AdrianaCabrera/MyOrthotics-2.0/images/image1.png

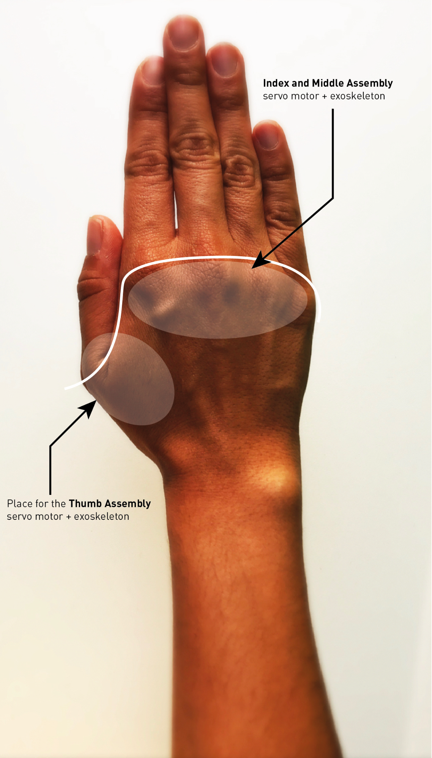
images/image1.png
