AdrianaCabrera/MyOrthotics-2.0/images/image2.png

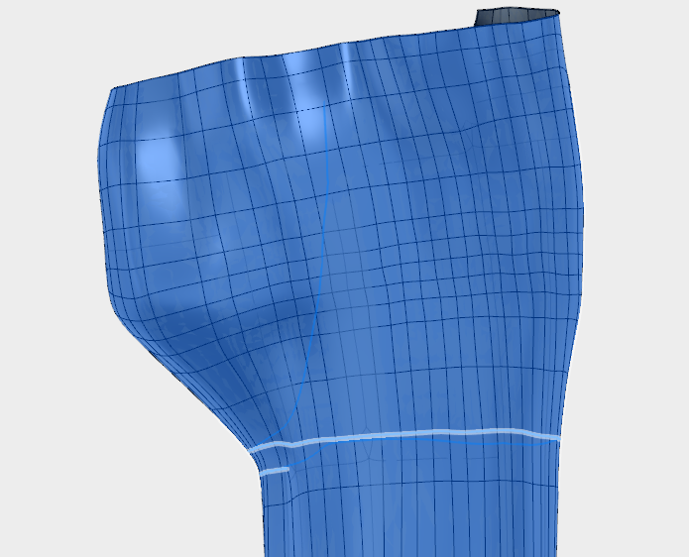
images/image2.png
