AdrianaCabrera/MyOrthotics-2.0/images/image3.jpg

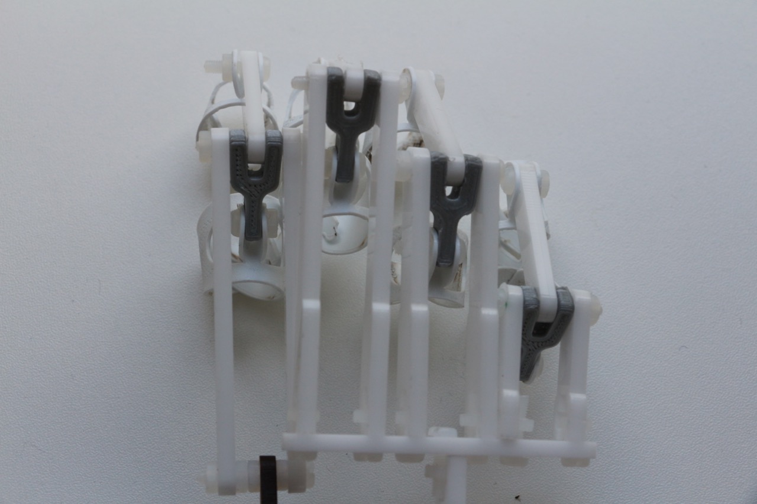
images/image3.jpg
