AdrianaCabrera/MyOrthotics-2.0/images/image4.png

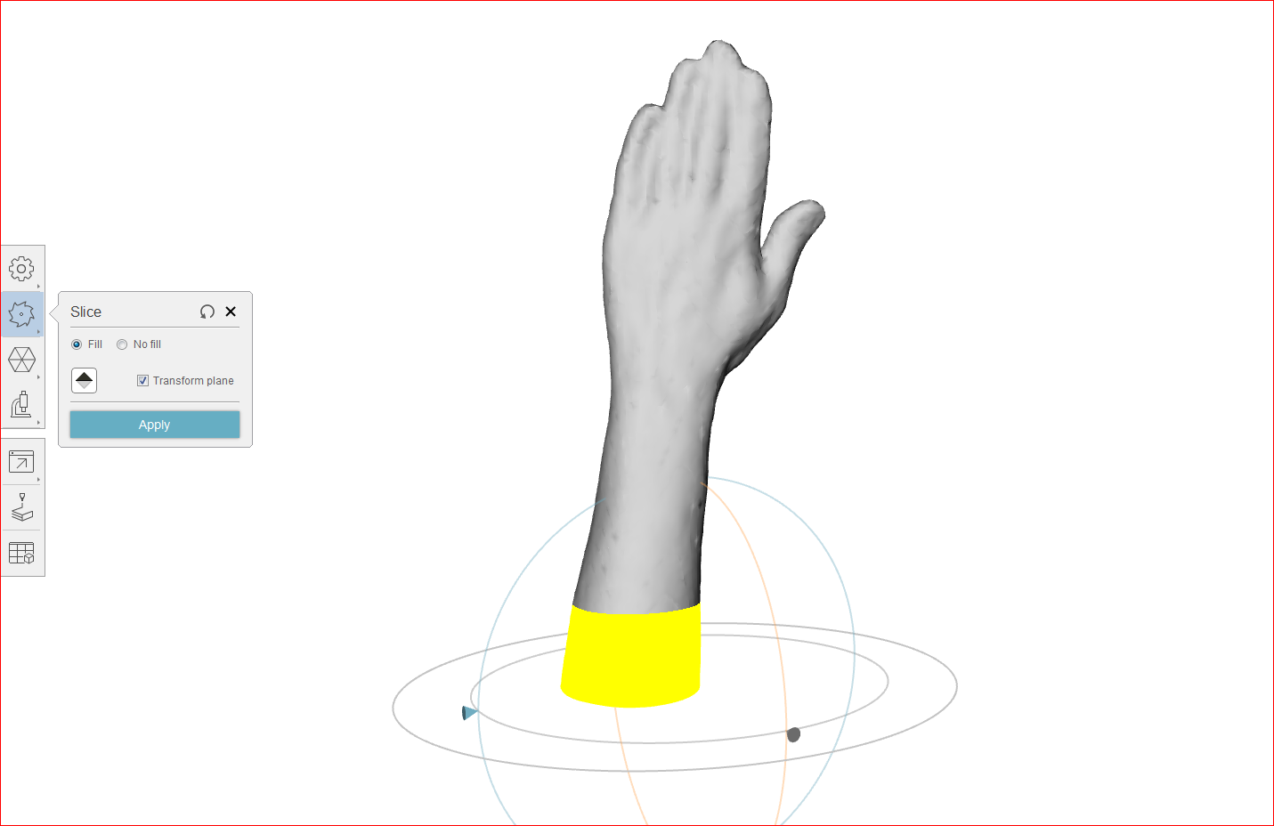
images/image4.png
