AdrianaCabrera/MyOrthotics-2.0/images/image6.png

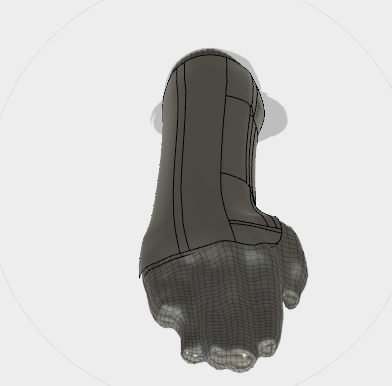
images/image6.png
