AdrianaCabrera/MyOrthotics-2.0/images/image7.png

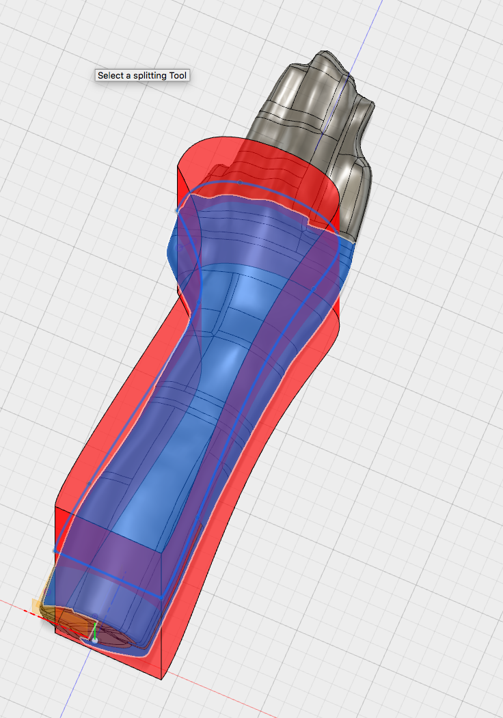
images/image7.png
