AdrianaCabrera/MyOrthotics-2.0/images/image8.png

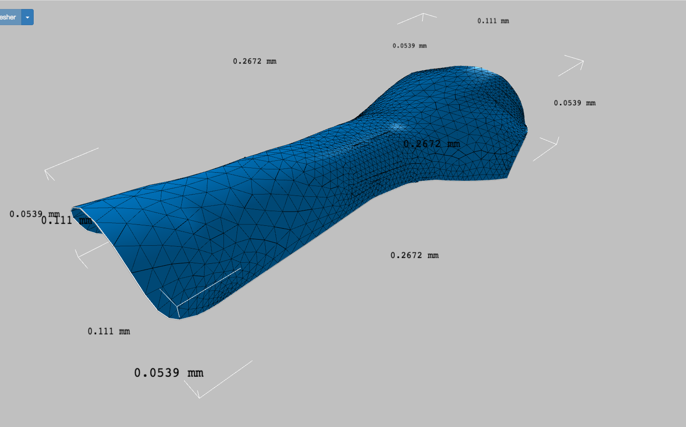
images/image8.png
