AdrianaCabrera/MyOrthotics-2.0/images/image9.jpg

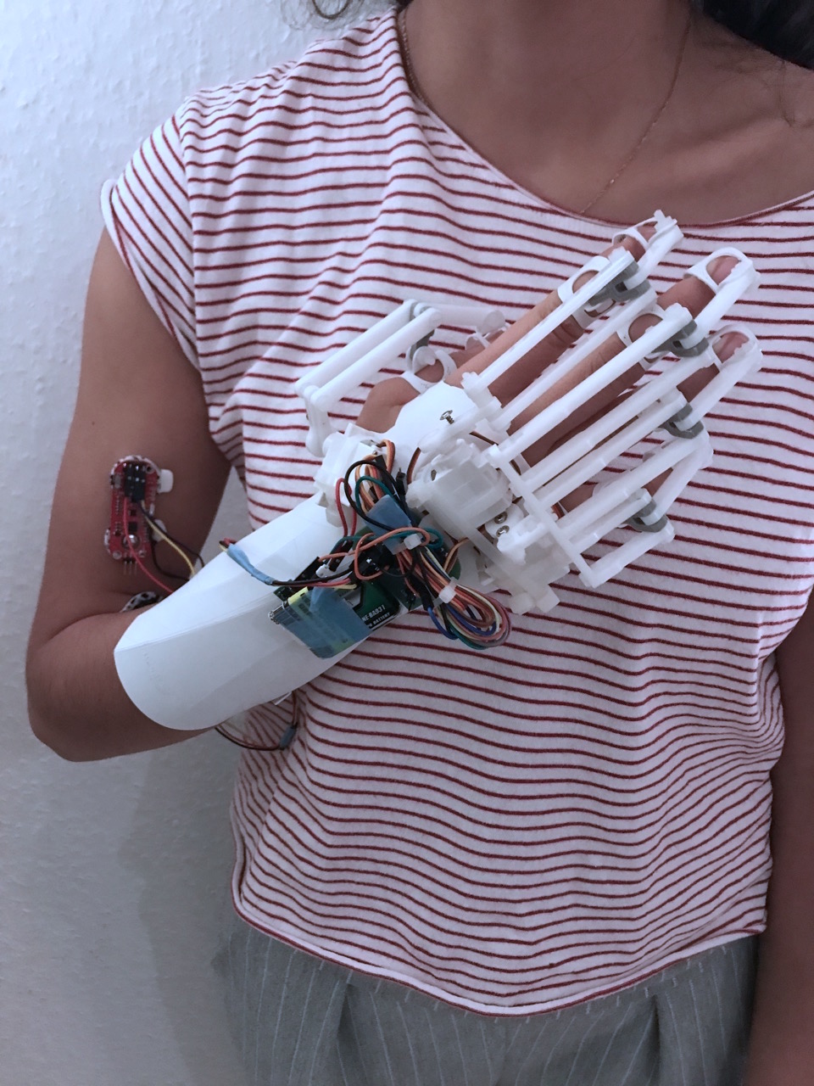
images/image9.jpg
