AdrianaCabrera/MyOrthotics-2.0/images/image10.png

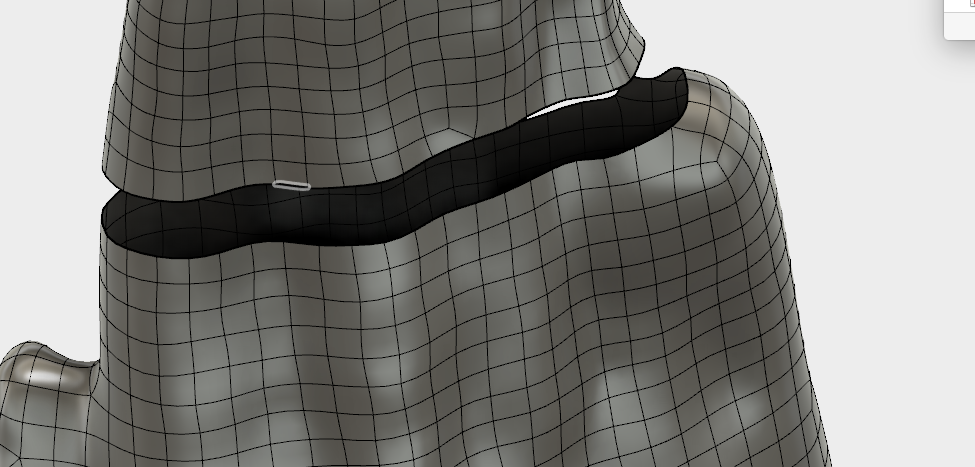
images/image10.png
