AdrianaCabrera/MyOrthotics-2.0/images/image11.png

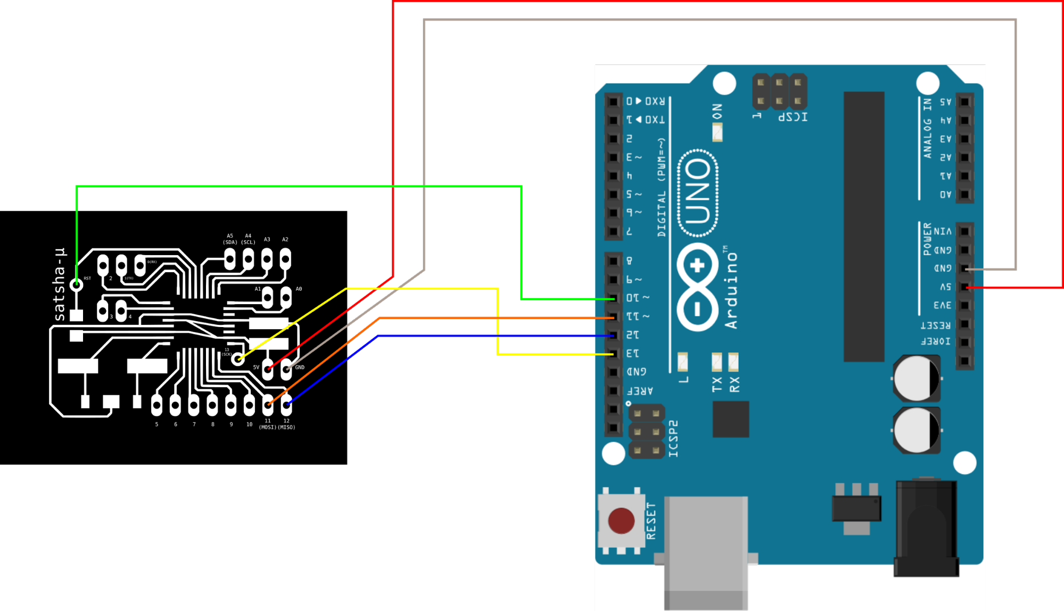
images/image11.png
