AdrianaCabrera/MyOrthotics-2.0/images/image12.png

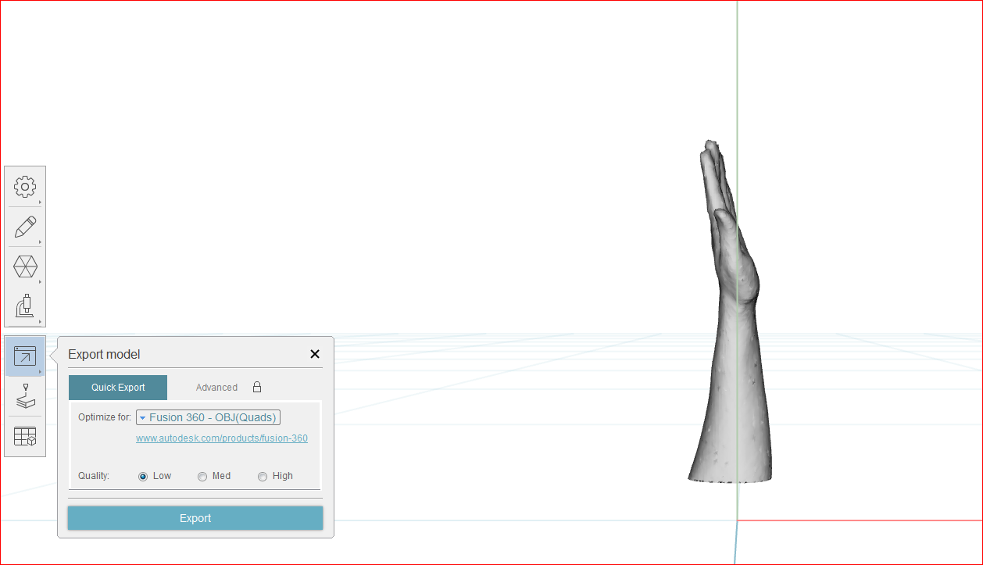
images/image12.png
