AdrianaCabrera/MyOrthotics-2.0/images/image13.jpg

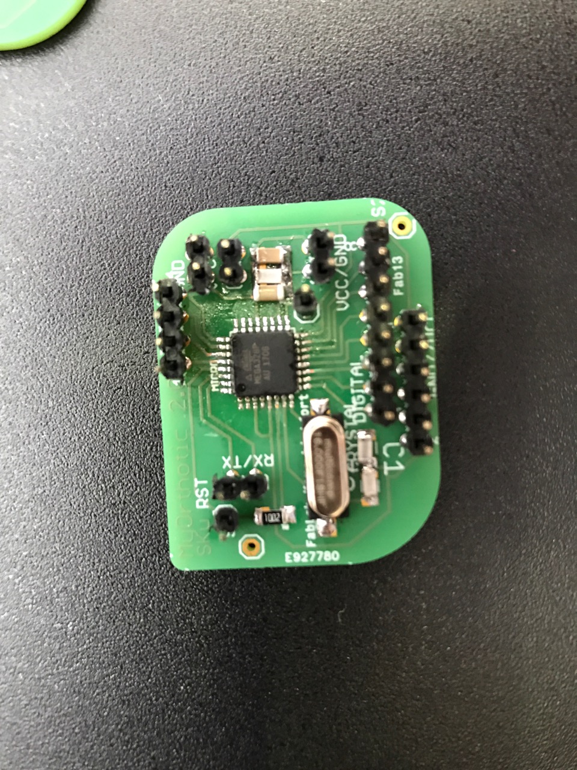
images/image13.jpg
