AdrianaCabrera/MyOrthotics-2.0/images/image14.jpg

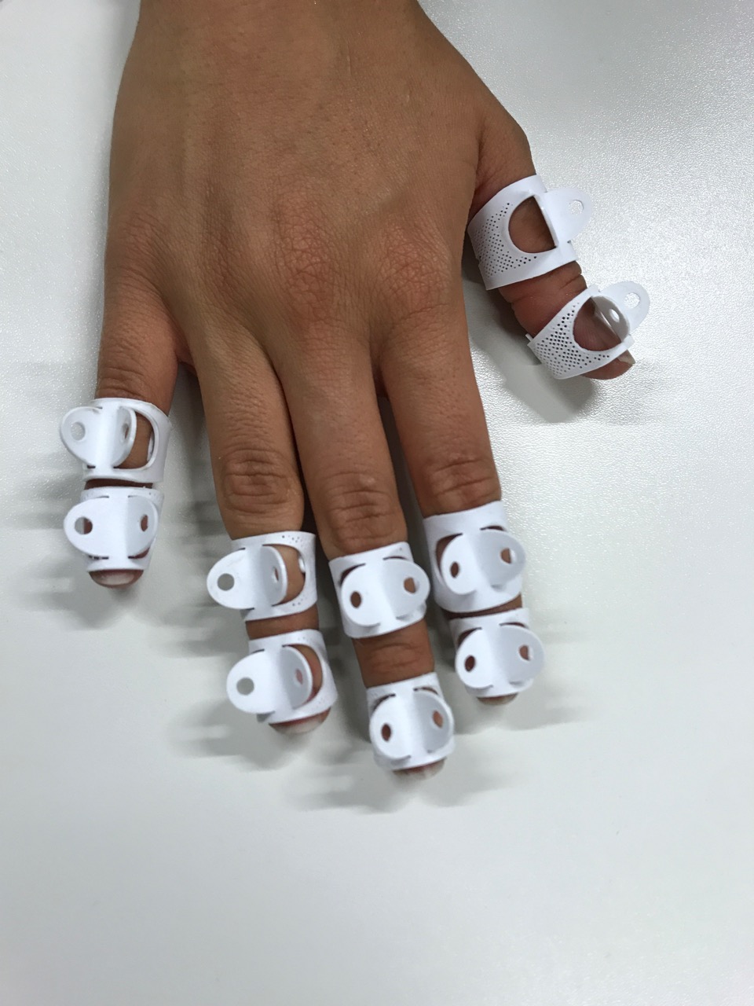
images/image14.jpg
