AdrianaCabrera/MyOrthotics-2.0/images/image15.png

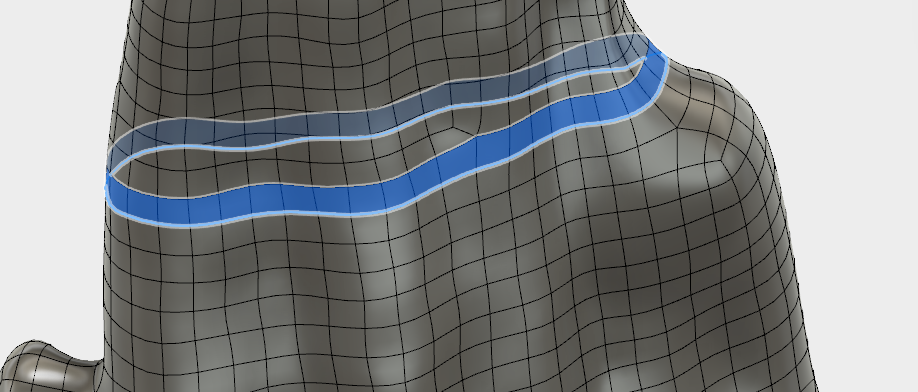
images/image15.png
