AdrianaCabrera/MyOrthotics-2.0/images/image16.png

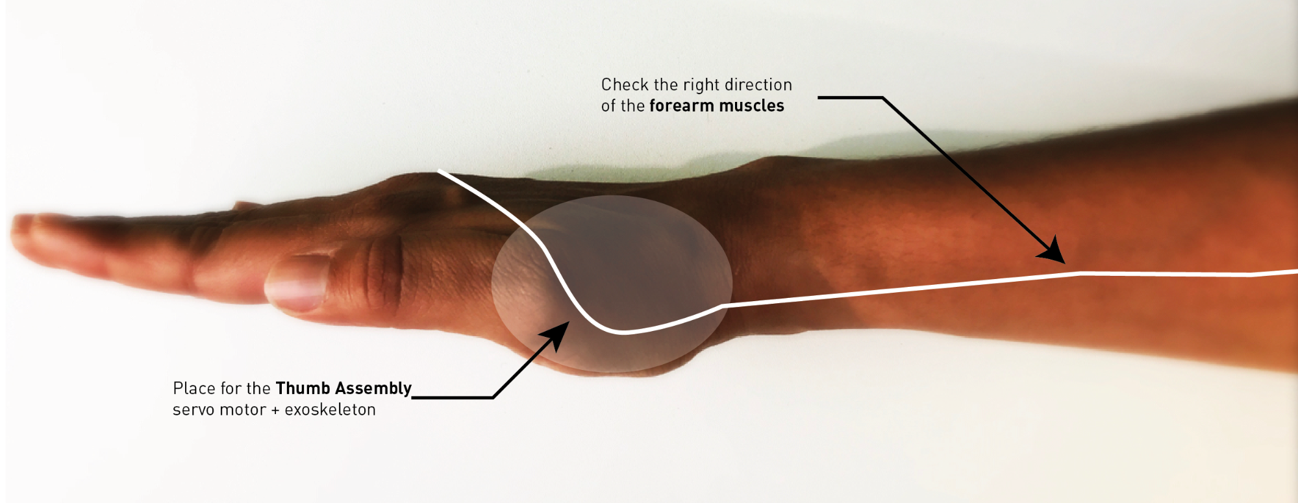
images/image16.png
