AdrianaCabrera/MyOrthotics-2.0/images/image17.png

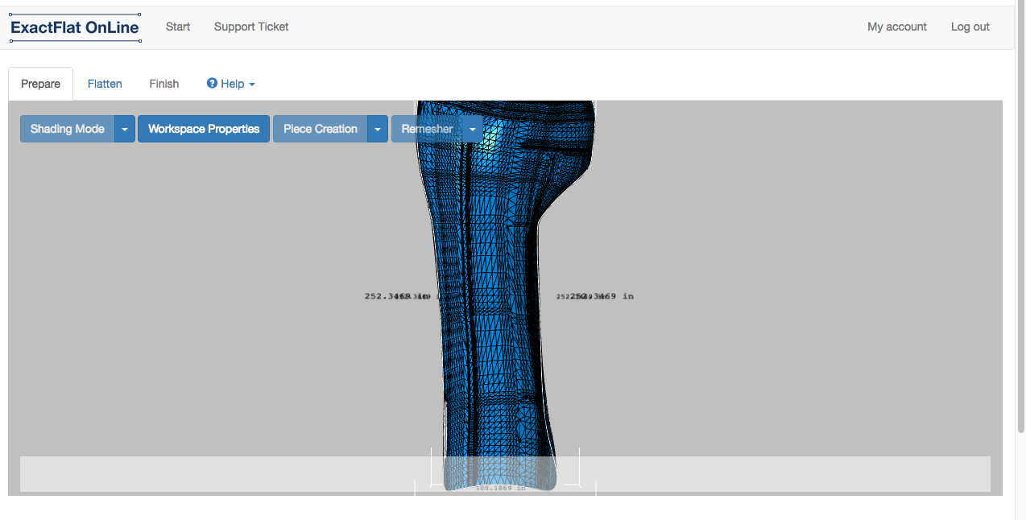
images/image17.png
