AdrianaCabrera/MyOrthotics-2.0/images/image19.png

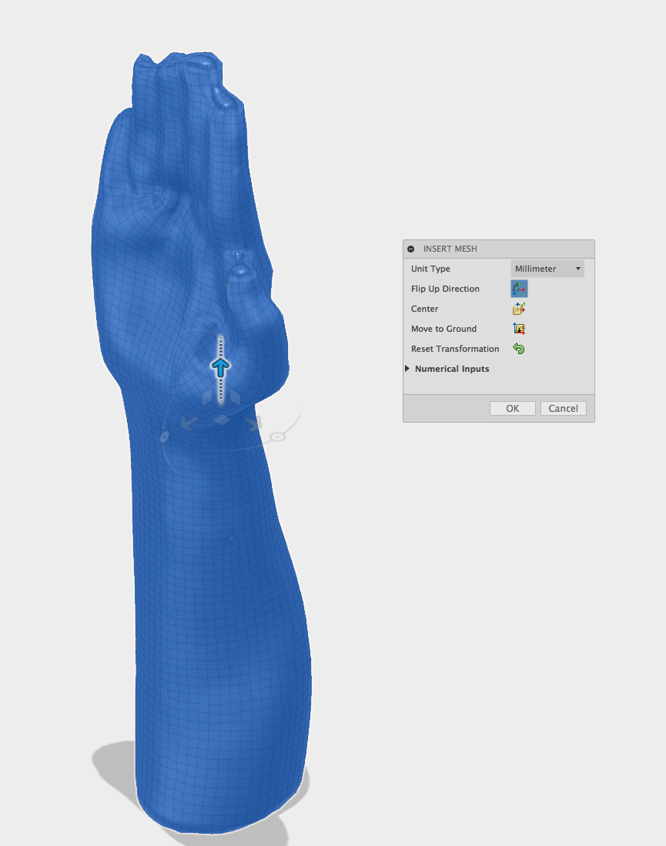
images/image19.png
