AdrianaCabrera/MyOrthotics-2.0/images/image20.png

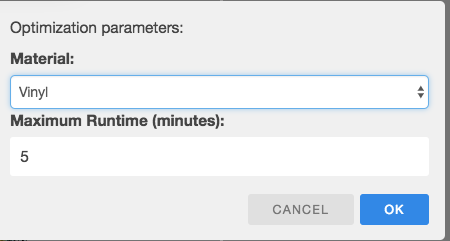
images/image20.png
