AdrianaCabrera/MyOrthotics-2.0/images/image21.jpg

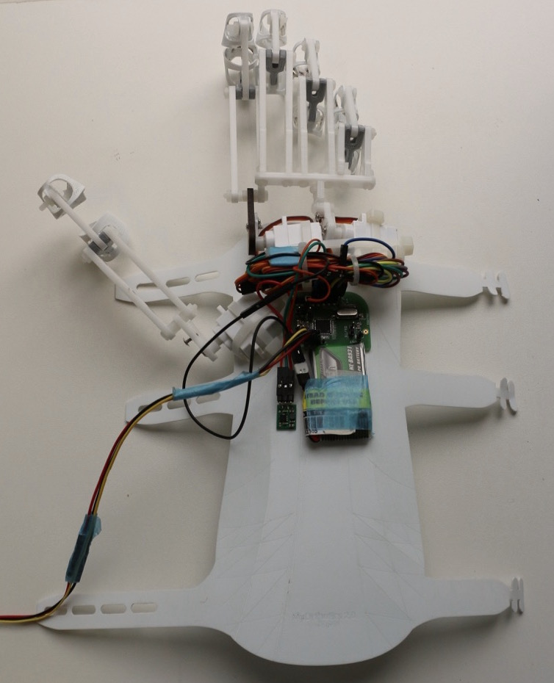
images/image21.jpg
