AdrianaCabrera/MyOrthotics-2.0/images/image22.png

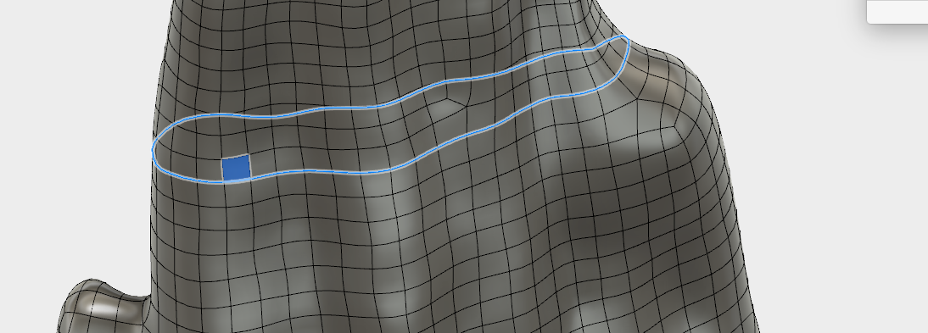
images/image22.png
