AdrianaCabrera/MyOrthotics-2.0/images/image23.jpg

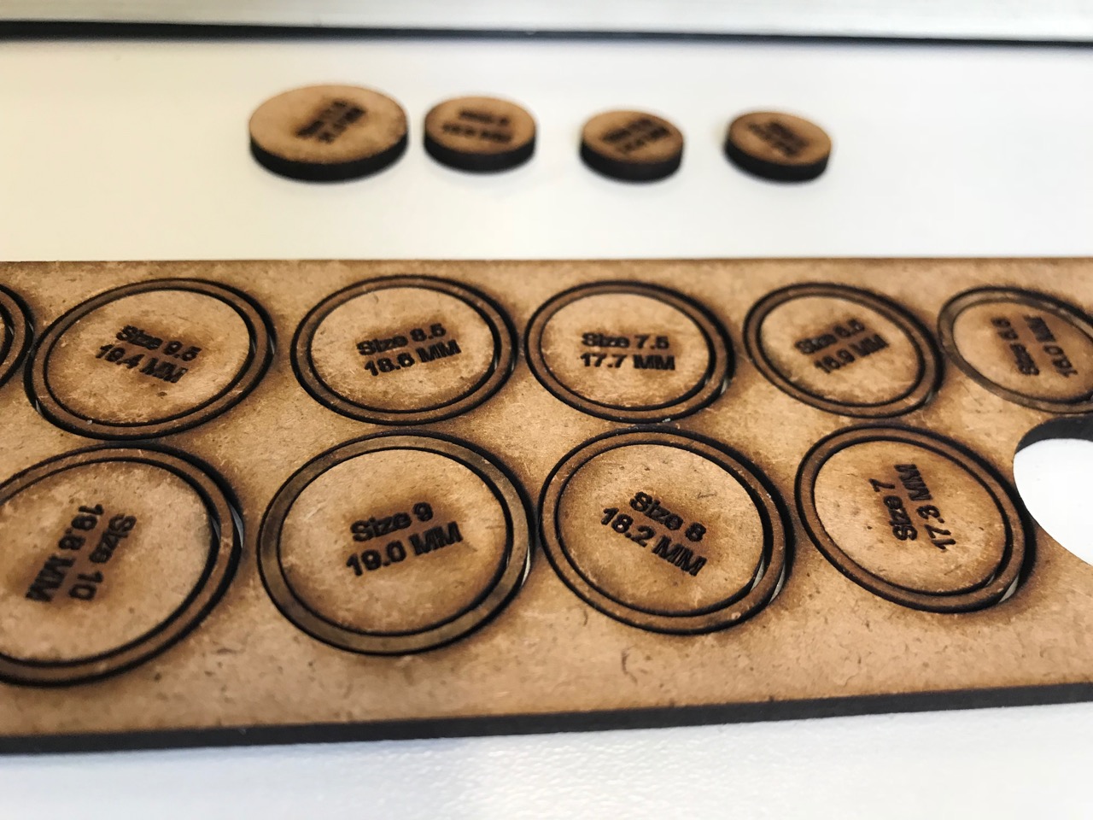
images/image23.jpg
