AdrianaCabrera/MyOrthotics-2.0/images/image24.jpg

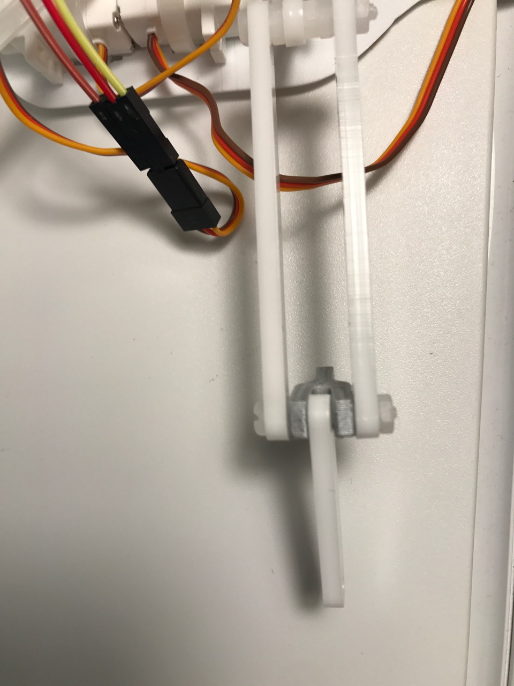
images/image24.jpg
