AdrianaCabrera/MyOrthotics-2.0/images/image25.png

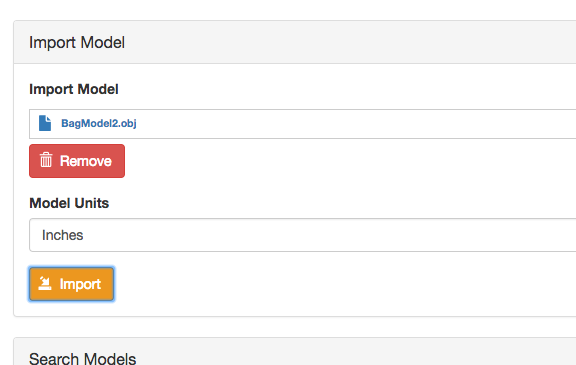
images/image25.png
