AdrianaCabrera/MyOrthotics-2.0/images/image26.png

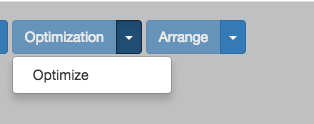
images/image26.png
