AdrianaCabrera/MyOrthotics-2.0/images/image28.jpg

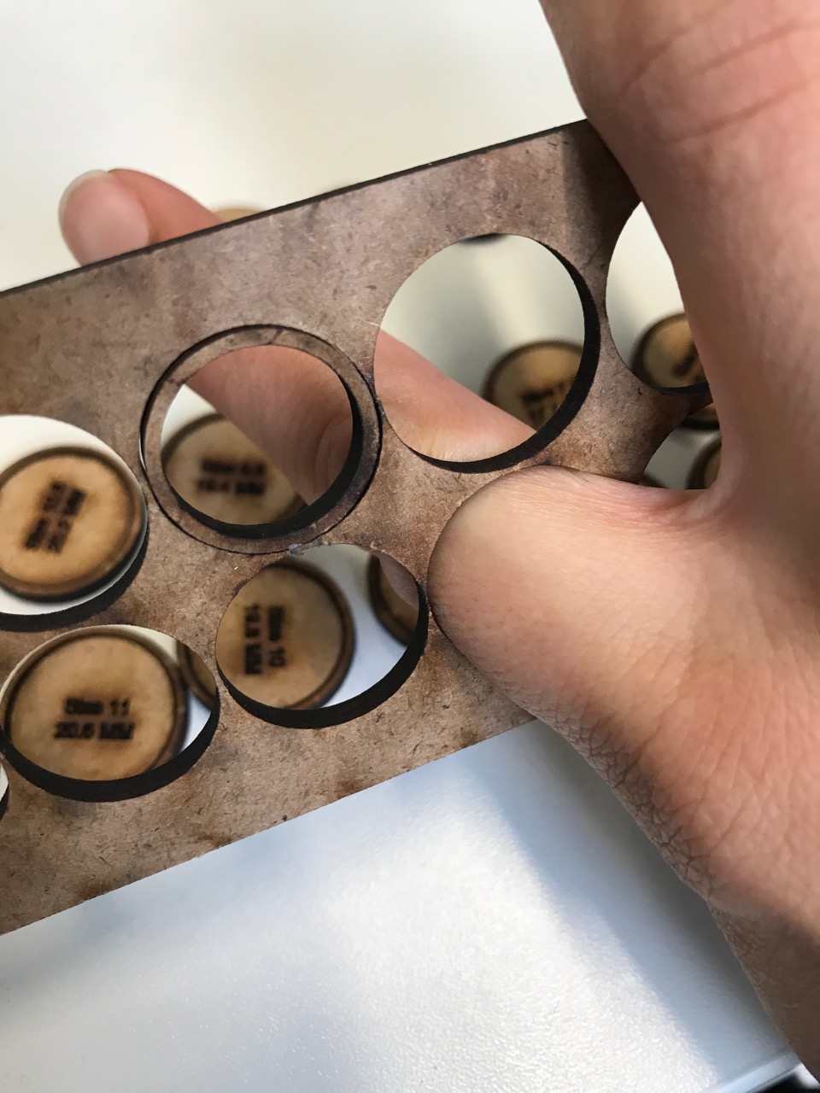
images/image28.jpg
