AdrianaCabrera/MyOrthotics-2.0/images/image29.jpg

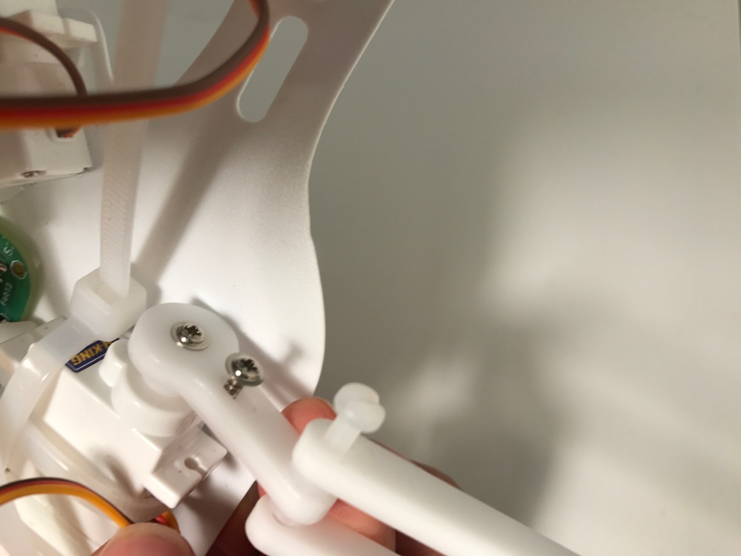
images/image29.jpg
