AdrianaCabrera/MyOrthotics-2.0/images/image30.png

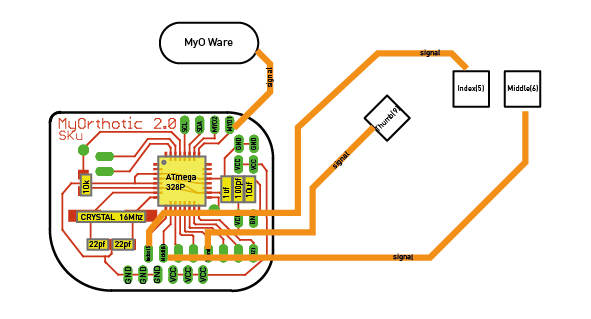
images/image30.png
