AdrianaCabrera/MyOrthotics-2.0/images/image31.jpg

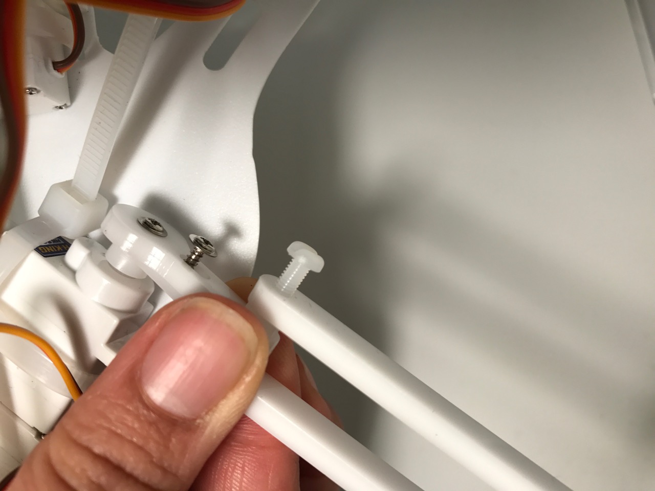
images/image31.jpg
