AdrianaCabrera/MyOrthotics-2.0/images/image32.png

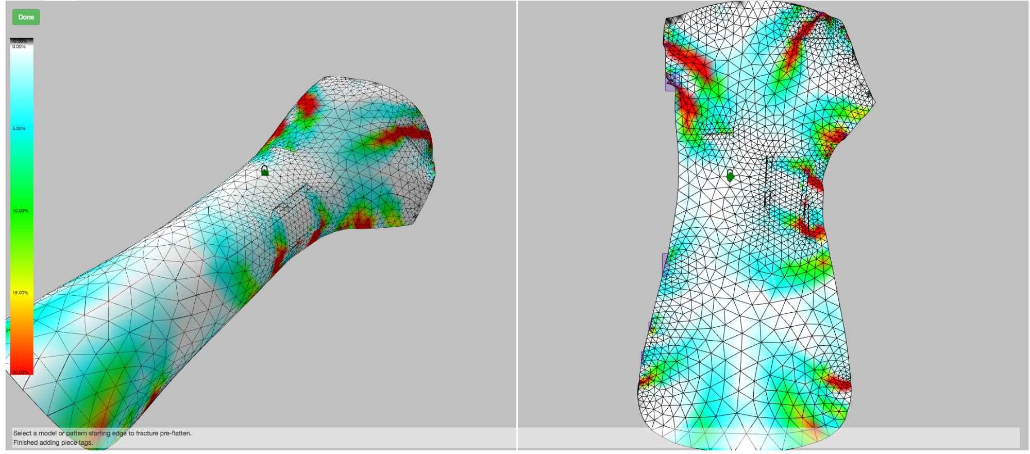
images/image32.png
