AdrianaCabrera/MyOrthotics-2.0/images/image33.jpg

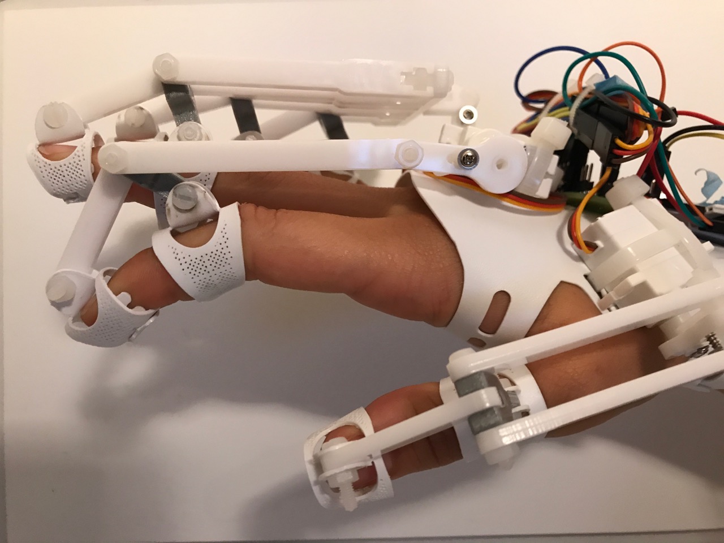
images/image33.jpg
