AdrianaCabrera/MyOrthotics-2.0/images/image34.png

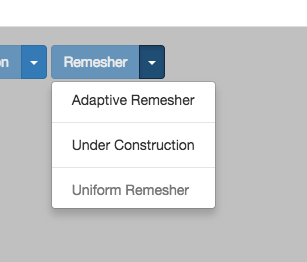
images/image34.png
