AdrianaCabrera/MyOrthotics-2.0/images/image35.png

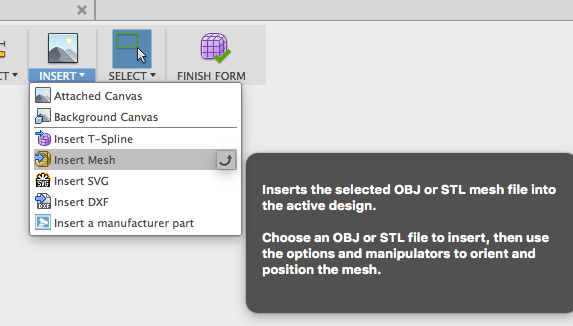
images/image35.png
