AdrianaCabrera/MyOrthotics-2.0/images/image36.png

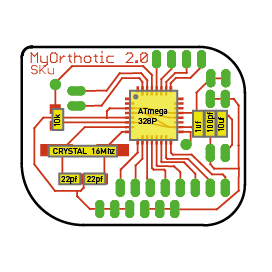
images/image36.png
