AdrianaCabrera/MyOrthotics-2.0/images/image37.jpg

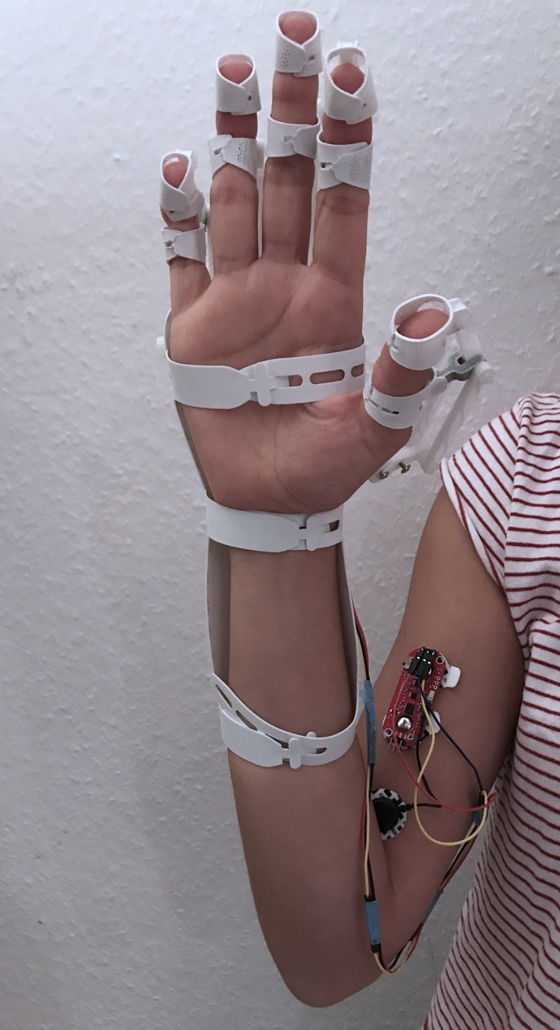
images/image37.jpg
