AdrianaCabrera/MyOrthotics-2.0/images/image38.jpg

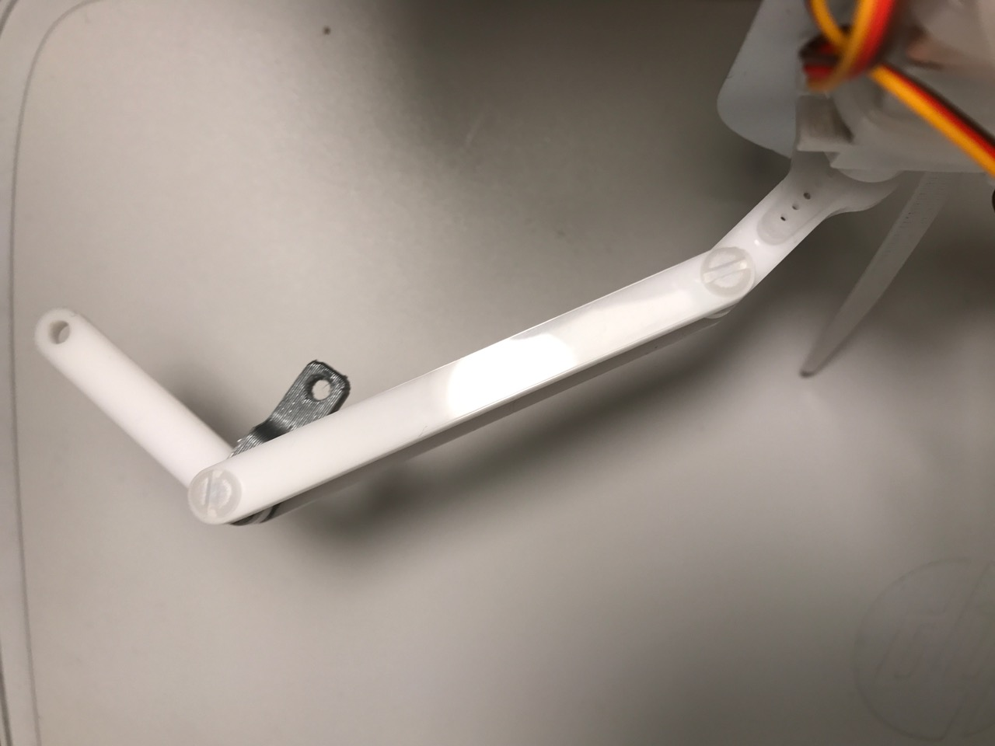
images/image38.jpg
