AdrianaCabrera/MyOrthotics-2.0/images/image39.png

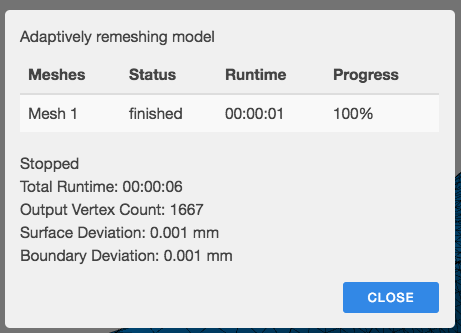
images/image39.png
