AdrianaCabrera/MyOrthotics-2.0/images/image41.jpg

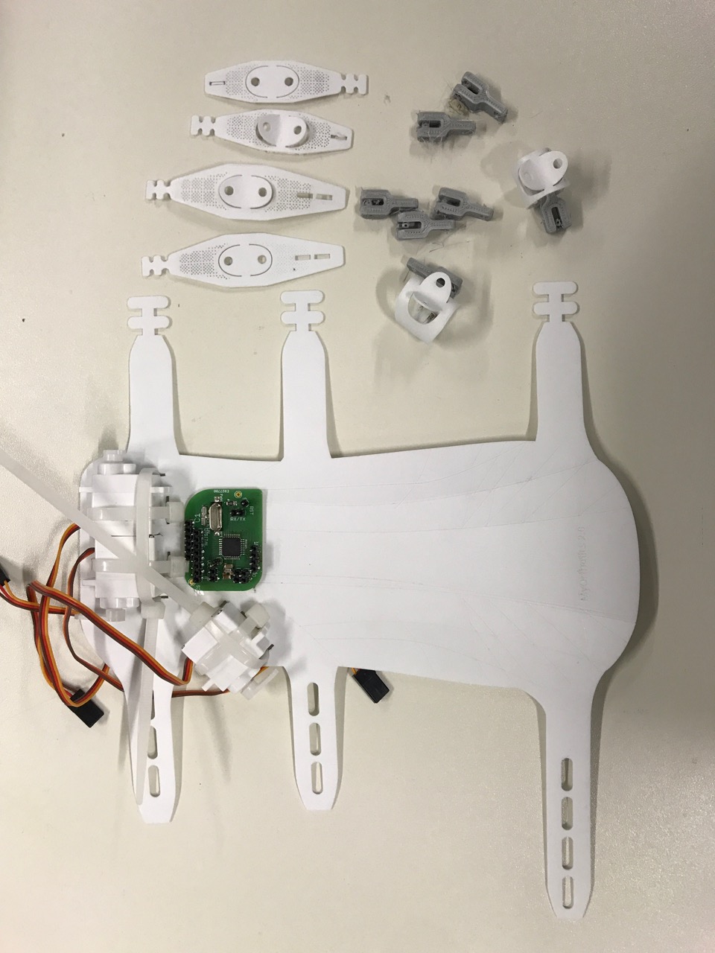
images/image41.jpg
