AdrianaCabrera/MyOrthotics-2.0/images/image42.png

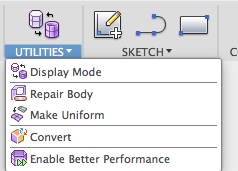
images/image42.png
